Pollyyaooo/Polly_PANG/Documentation/PANG_Curcuit Diagram.kicad_sch

## KiCad design Documentation/PANG_Curcuit Diagram.kicad_sch (2025-12-03)

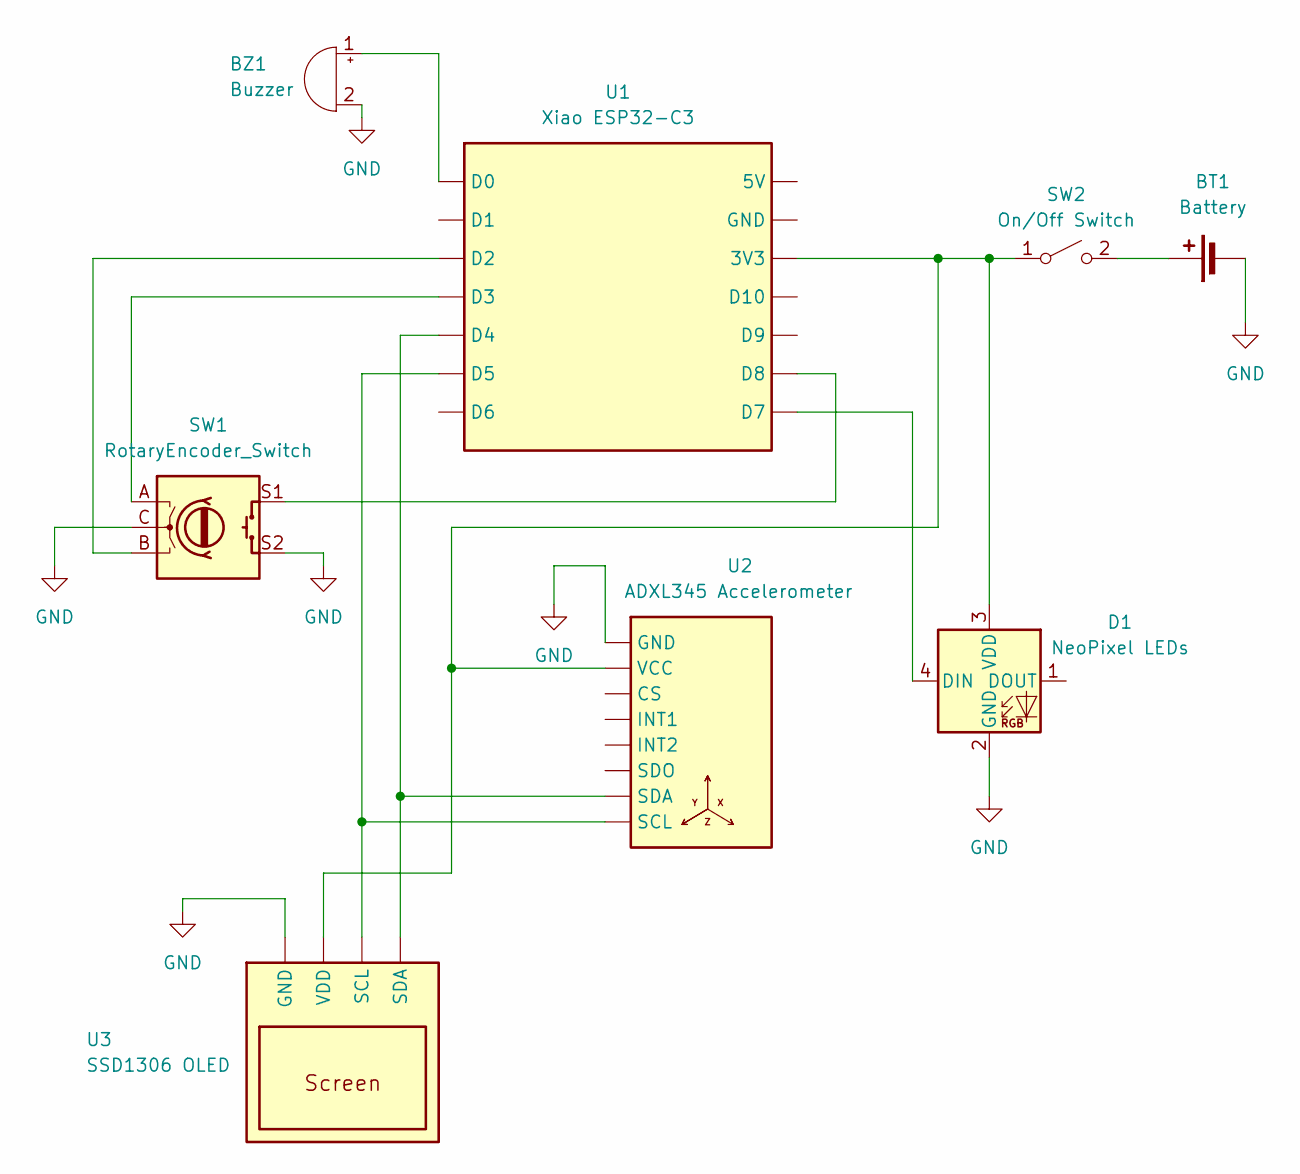
[picture p5: schematic PANG_Curcuit Diagram.kicad_sch]

Parts:
BT1: Battery
BZ1: Buzzer
D1: NeoPixel LEDs
SW1: RotaryEncoder_Switch
SW2: On/Off Switch
U1: Xiao ESP32-C3; Arduino_Nano
U2: ADXL345 Accelerometer; Kionix_LGA-12_2x2mm_P0.5mm_LayoutBorder2x4y
U3: SSD1306 OLED; EA_T123X-I2C

Connections:
GND: BT1.2 (-), BZ1.2 (-), D1.2 (GND), SW1.C, SW1.S2, U2., U3.
unnamed: BT1.1 (+), SW2.2 (B)
unnamed: BZ1.1 (+), U1.
unnamed: D1.3 (VDD), SW2.1 (A), U1., U2., U3.
unnamed: D1.4 (DIN), U1.
unnamed: SW1.A, U1.
unnamed: SW1.B, U1.
unnamed: SW1.S1, U1.
unnamed: U1., U2., U3.
